NicheElectronics/LM53635-Q1-Wide-Input-DC-DC-Converter/pcb-design/emi-filter/EMI-Filter-Schematic.png

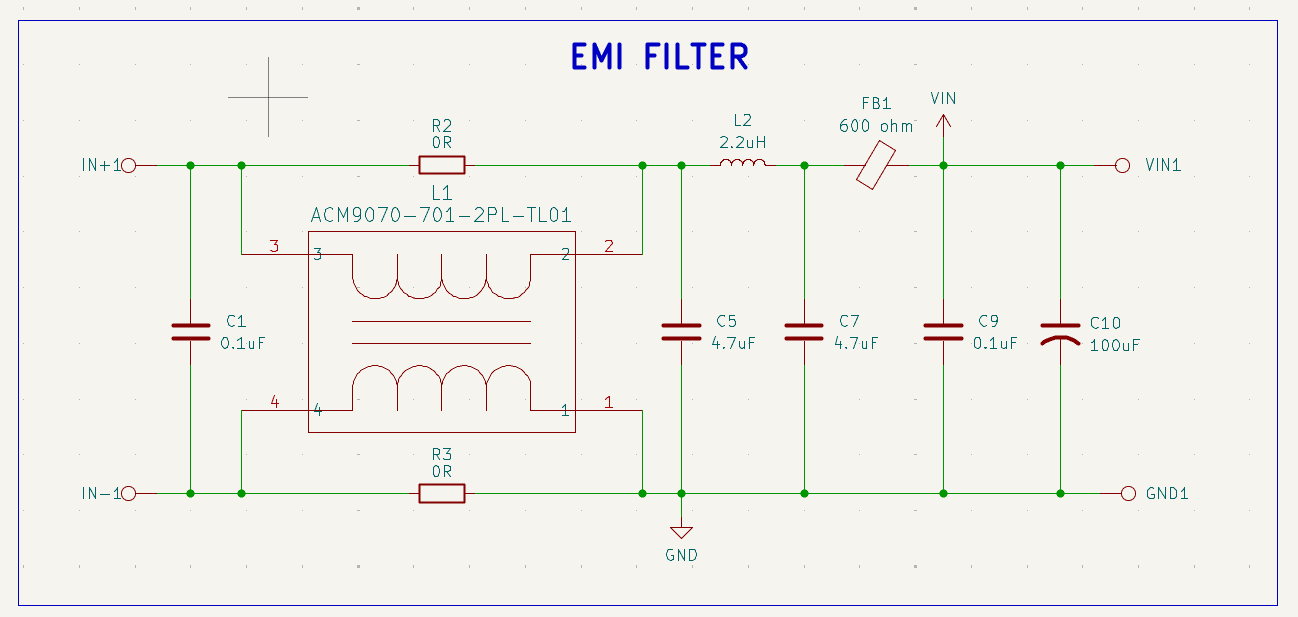
pcb-design/emi-filter/EMI-Filter-Schematic.png
