NicheElectronics/LM53635-Q1-Wide-Input-DC-DC-Converter/pcb-design/layers/L1-Top-Power-Signal-GND-Pour.png

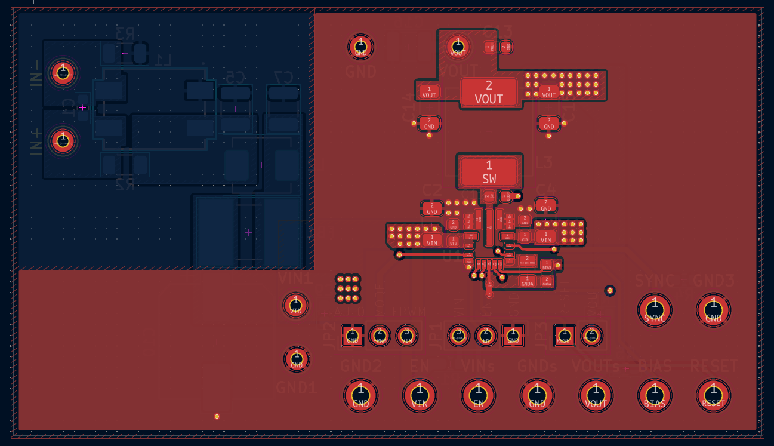
pcb-design/layers/L1-Top-Power-Signal-GND-Pour.png
