NicheElectronics/LM53635-Q1-Wide-Input-DC-DC-Converter/pcb-design/stackup/JLC04161H-2116B-4-Layer-Stackup.png

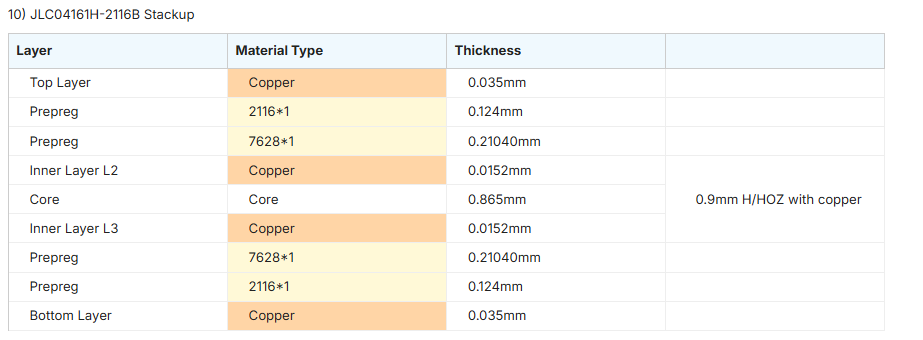
pcb-design/stackup/JLC04161H-2116B-4-Layer-Stackup.png
