NicheElectronics/LM53635-Q1-Wide-Input-DC-DC-Converter/simulation/pspice-project/LM53635-Q1-PSpice/LM536355-Q1_PSPICE_TRANS/LM536355-Q1_TRANS.png

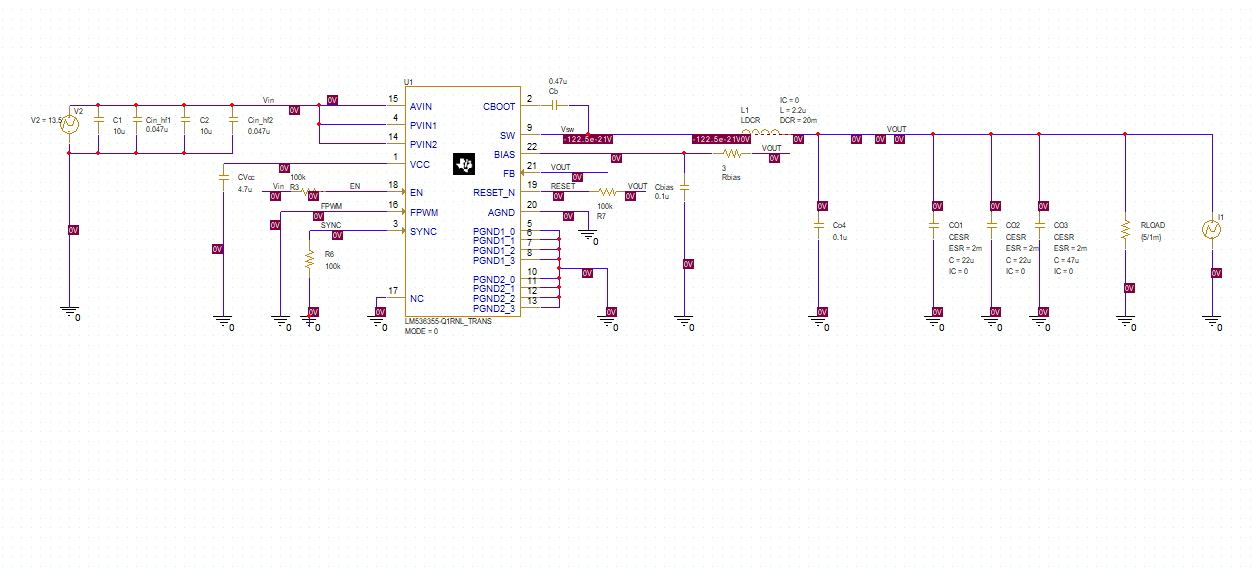
simulation/pspice-project/LM53635-Q1-PSpice/LM536355-Q1_PSPICE_TRANS/LM536355-Q1_TRANS.png
